eshazen/hex-calc/3D/lcd.scad

//
// 16x2 LCD
//

lcd_wid = 80;
lcd_len = 31;

lcd_thk = 13.5;

module lcd() {
     cube( [lcd_wid, lcd_len, lcd_thk]);
}

     
