eshazen/hex-calc/src/calc_hw/led.h

// calculator LEDs on PB0, 1
#define LED_DDR DDRB
#define LED_BIT_D1 0
#define LED_BIT_D2 1
#define LED_PORT PORTB

void led_init();
void set_led( int num, int state);
